linuxplayground/6502-retro/software/apps/05-snake/main.h

#define VDP_PATTERN_TABLE          0x0000
#define VDP_NAME_TABLE             0x3800
#define VDP_SPRITE_ATTRIBUTE_TABLE 0x3b00
#define VDP_COLOR_TABLE            0x2000
#define VDP_SPRITE_PATTERN_TABLE   0x1800

#define head_up    0x01
#define head_dn    0x02
#define head_lt    0x03
#define head_rt    0x04
#define applechar  0x05

#define BUFFER_SIZE 0x1000
